shrhdk/theta-remote-release/src/button.cpp

/*
 * Copyright (c) 2016 Hideki Shiro
 */

#include "button.h"
#include "arduino.h"

Button::Button(int port) : port(port) { pinMode(port, INPUT); }

bool Button::isPressed() { return digitalRead(port) == LOW; }
